Anti-AliasLabs/gps_shoes/nplh/ChooseHome/data/pointershoe.gif

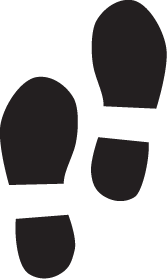
nplh/ChooseHome/data/pointershoe.gif
